bitcoin-ring/Bolty/tardata.cpp

#include <Arduino.h>

int fsversion = 12;
unsigned char data_tar[] = {
  0x1f, 0x8b, 0x08, 0x00, 0x00, 0x00, 0x00, 0x00, 0x00, 0x03, 0xec, 0x3c,
  0x09, 0x98, 0x14, 0xd5, 0x99, 0xe3, 0x6a, 0x82, 0x8e, 0x4a, 0x48, 0x42,
  0xd4, 0x15, 0xcd, 0x3e, 0x5a, 0x67, 0x99, 0x81, 0xa9, 0x9a, 0xae, 0x3e,
  0xa6, 0x67, 0x7a, 0x0e, 0x03, 0xcc, 0x4c, 0x1c, 0x41, 0x20, 0x03, 0x88,
  0x20, 0x08, 0x35, 0xd5, 0xaf, 0xbb, 0x6b, 0xa6, 0xba, 0xaa, 0xad, 0xaa,
  0x9e, 0x83, 0x11, 0x0d, 0x0a, 0xa2, 0x08, 0x12, 0x8f, 0x98, 0x2f, 0xab,
  0xac, 0x5f, 0x12, 0x35, 0x21, 0x89, 0x44, 0xd6, 0xdb, 0xe8, 0xba, 0x6a,
  0x42, 0x3c, 0x36, 0x51, 0xc3, 0x46, 0xd4, 0xe0, 0x15, 0xd4, 0x84, 0xe8,
  0xba, 0x78, 0x86, 0x8d, 0x7e, 0xb0, 0xff, 0x3b, 0xaa, 0xbb, 0xaa, 0x8f,
  0x39, 0x64, 0x06, 0x63, 0x96, 0x1a, 0xe8, 0xae, 0x7a, 0xf5, 0xbf, 0xff,
  0xfd, 0xff, 0xff, 0xfe, 0xf3, 0xd5, 0xab, 0x16, 0x6b, 0xca, 0xc6, 0xfc,
  0xf0, 0xc3, 0x11, 0x89, 0x84, 0xc9, 0xb7, 0x14, 0x09, 0xfb, 0xdd, 0xdf,
  0xce, 0x51, 0x26, 0x85, 0xc2, 0xa1, 0x50, 0x30, 0x5c, 0x1b, 0xf4, 0x87,
  0xca, 0xfc, 0x92, 0x3f, 0x10, 0x0a, 0x97, 0xa1, 0xf0, 0xd8, 0x93, 0x56,
  0x56, 0x96, 0xb1, 0x6c, 0xd9, 0x44, 0xa8, 0xcc, 0x4e, 0xaa, 0x9a, 0x31,
  0x08, 0xdc, 0x50, 0xf7, 0x3f, 0xa3, 0x87, 0x58, 0x63, 0x61, 0x3b, 0x93,
  0x16, 0x93, 0x76, 0x4a, 0x1b, 0xab, 0x31, 0xc8, 0x04, 0xd7, 0xd6, 0x86,
  0x4a, 0xcc, 0x7f, 0xc0, 0x5f, 0x1b, 0x20, 0xf3, 0x1f, 0x0a, 0x44, 0x22,
  0x91, 0x50, 0xad, 0x04, 0x7a, 0x22, 0x05, 0x88, 0x1a, 0x20, 0xff, 0x58,
  0x11, 0xe4, 0x3e, 0xfe, 0x9f, 0xcf, 0x7f, 0xe3, 0xe4, 0x96, 0xb9, 0x33,
  0x17, 0x2c, 0x9e, 0xd7, 0x8a, 0x88, 0x06, 0x34, 0x97, 0x37, 0x3a, 0x5f,
  0x58, 0x8e, 0xc1, 0x97, 0xa6, 0xea, 0xdd, 0xc8, 0xc4, 0x5a, 0x93, 0xcf,
  0xb2, 0xfb, 0x35, 0x6c, 0x25, 0x31, 0xb6, 0x7d, 0x28, 0x69, 0xe2, 0x38,
  0x6f, 0x11, 0x15, 0xcb, 0xf2, 0x35, 0x97, 0x97, 0x37, 0x5a, 0x8a, 0xa9,
  0xa6, 0x6d, 0xa4, 0xc9, 0x7a, 0x22, 0x23, 0x27, 0x70, 0x93, 0xaf, 0x4b,
  0xee, 0x91, 0x59, 0xa3, 0x0f, 0x59, 0xa6, 0x02, 0xf0, 0x54, 0xd1, 0xba,
  0x08, 0x78, 0x63, 0x0d, 0xbb, 0xd3, 0x3c, 0x78, 0xbf, 0xe6, 0x72, 0x04,
  0x87, 0x86, 0x6d, 0xd4, 0x9b, 0x36, 0x0d, 0x1b, 0x35, 0x21, 0x9f, 0xaf,
  0x21, 0xd7, 0x96, 0x34, 0x2c, 0xda, 0x56, 0xd1, 0x2b, 0x6b, 0xd0, 0xb0,
  0x9c, 0x5c, 0x57, 0xb8, 0x01, 0xd4, 0xb8, 0x0a, 0xb3, 0xcb, 0x40, 0xd8,
  0xb9, 0x73, 0xbb, 0x07, 0xe6, 0xbc, 0x37, 0x63, 0x6a, 0x1c, 0xa5, 0x8b,
  0x9e, 0x14, 0x86, 0x1e, 0x4a, 0x52, 0x36, 0x81, 0xdc, 0x26, 0x5f, 0xc6,
  0x8e, 0x0b, 0x75, 0x94, 0x60, 0x2e, 0x90, 0x4e, 0x23, 0xd6, 0x0f, 0x5f,
  0x31, 0xb5, 0x07, 0x29, 0x9a, 0x6c, 0x59, 0x4d, 0xbe, 0xb8, 0x61, 0xa6,
  0x08, 0x84, 0xaa, 0xa7, 0x33, 0x36, 0xb2, 0xfb, 0xd3, 0x18, 0x25, 0xd5,
  0x58, 0x0c, 0xeb, 0x48, 0x8d, 0x35, 0xf9, 0xba, 0x71, 0xbf, 0xe5, 0xa3,
  0xad, 0x4d, 0x3e, 0x9f, 0xb7, 0xa3, 0x85, 0x35, 0xac, 0xd8, 0x14, 0x39,
  0xb4, 0x7a, 0xef, 0x91, 0xd1, 0x90, 0x56, 0xd8, 0x81, 0x8b, 0xc4, 0xdd,
  0x9a, 0xc2, 0x00, 0x48, 0xc7, 0xa2, 0x02, 0xf6, 0xa1, 0xe6, 0x46, 0xd9,
  0xb9, 0xa7, 0x6a, 0xce, 0x64, 0x31, 0x33, 0xf7, 0x35, 0xd3, 0xaf, 0xc6,
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
};
unsigned int data_tar_len = 9245;
